normgiff/Masters/DUTBoard/DUTBoardPinout.png

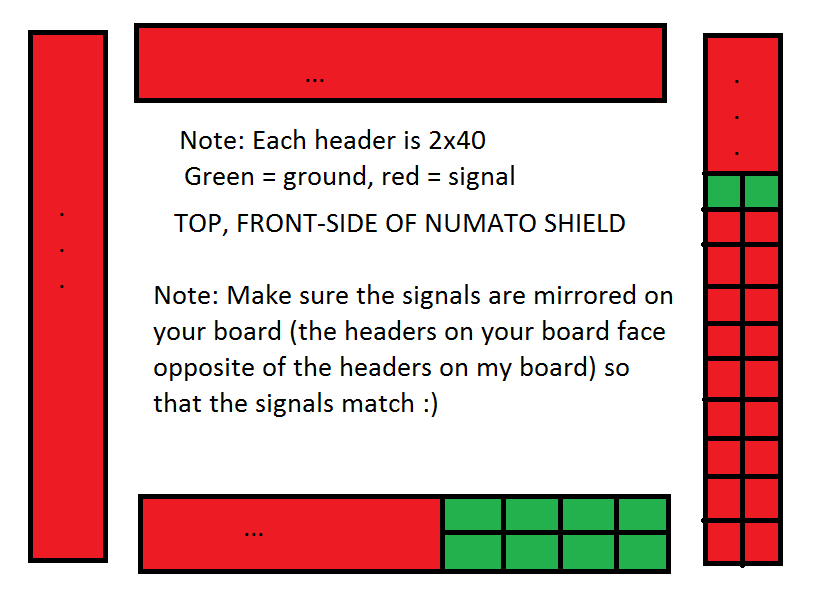
DUTBoard/DUTBoardPinout.png
