normgiff/Masters/explorations/clocking/clocking_proposal.png

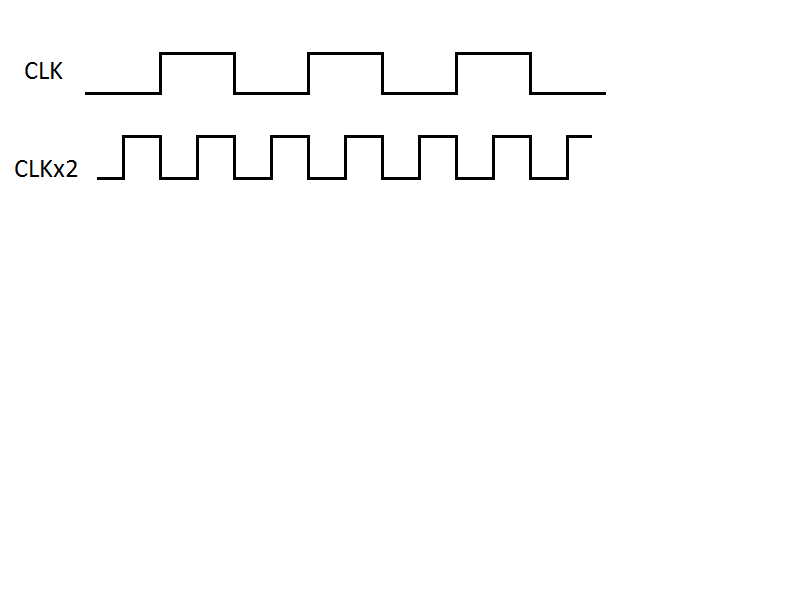
explorations/clocking/clocking_proposal.png
