normgiff/Masters/explorations/clocking/Dynamically_Reconfigurable_PLL.png

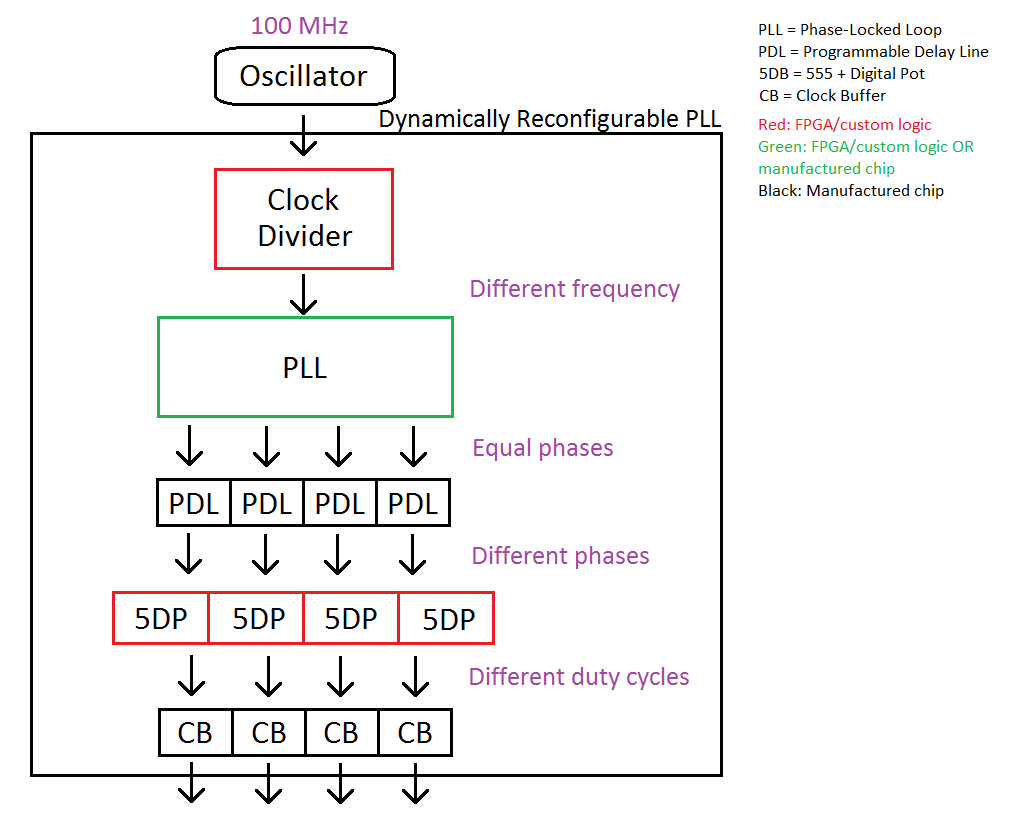
explorations/clocking/Dynamically_Reconfigurable_PLL.png
