normgiff/Masters/explorations/force_formats/force_formats_design_concept_2.png

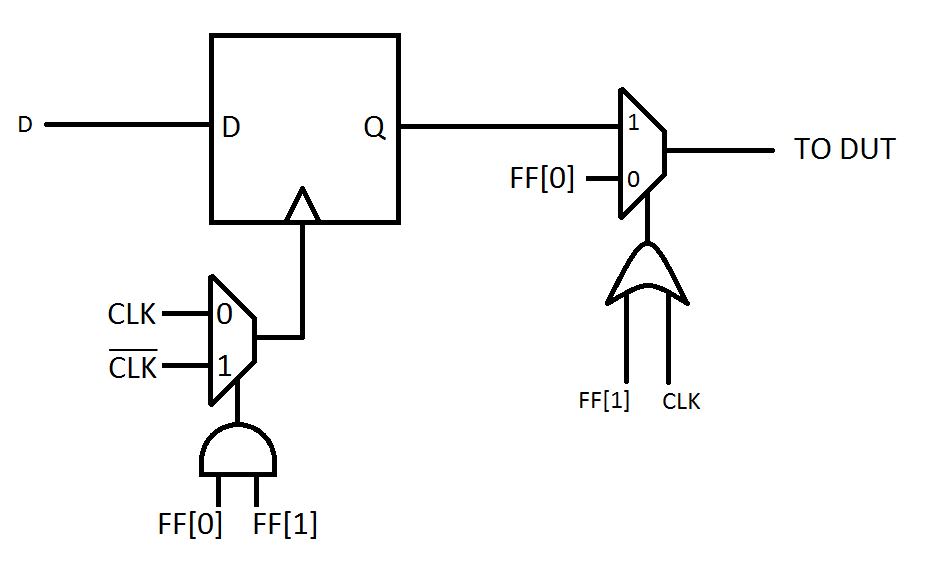
explorations/force_formats/force_formats_design_concept_2.png
