normgiff/Masters/explorations/force_formats/oddr2_idea.png

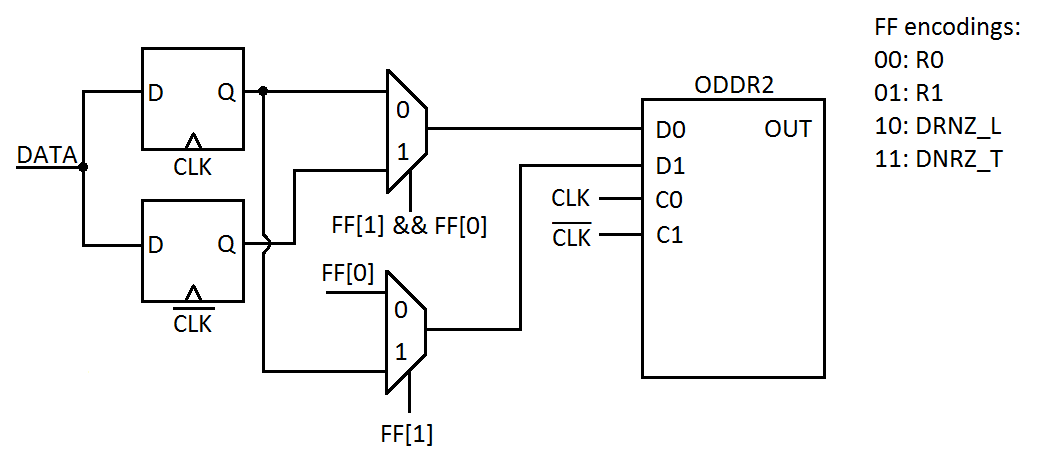
explorations/force_formats/oddr2_idea.png
