normgiff/Masters/explorations/high_level_diagram_1.png

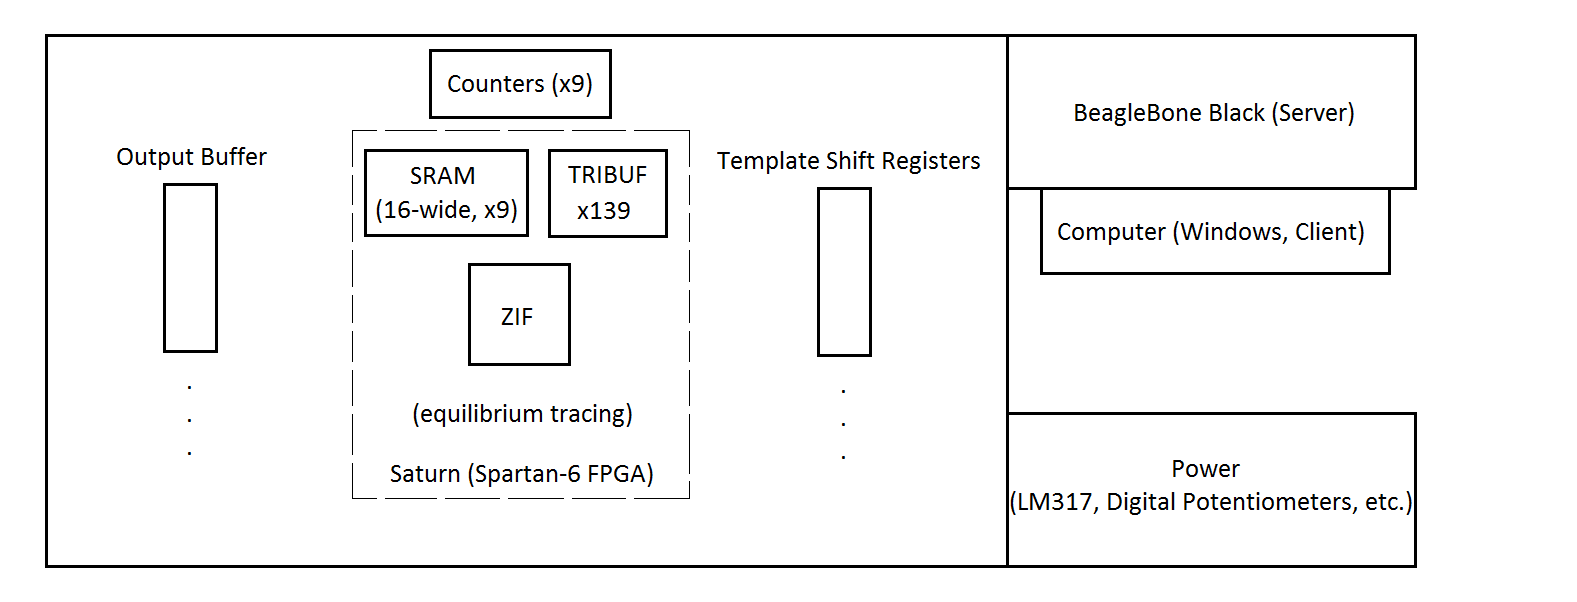
explorations/high_level_diagram_1.png
