normgiff/Masters/explorations/power/idea1.bmp

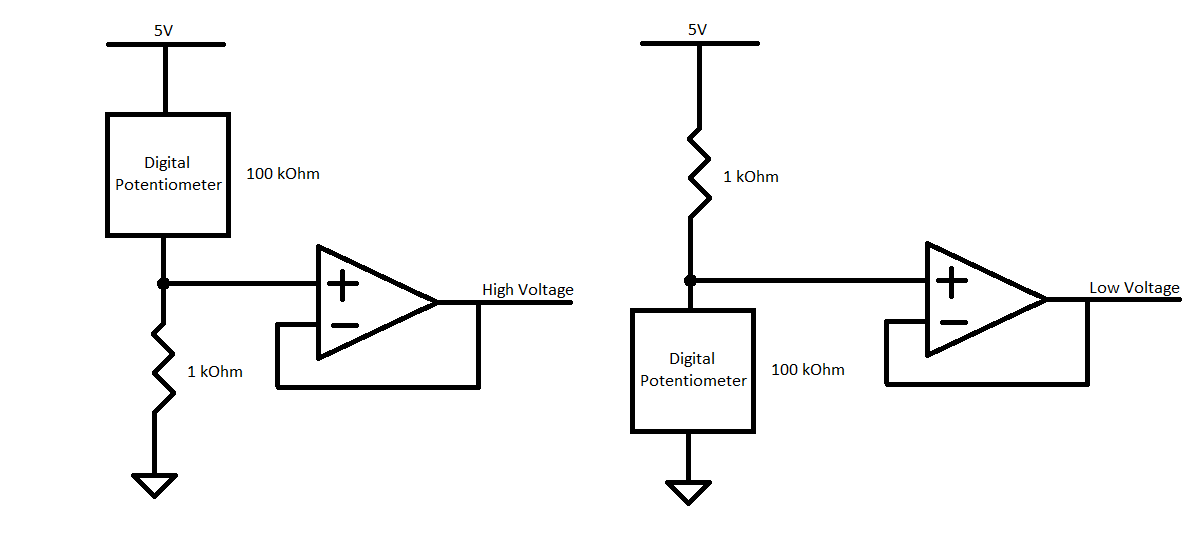
explorations/power/idea1.bmp
