normgiff/Masters/explorations/power/idea2.bmp

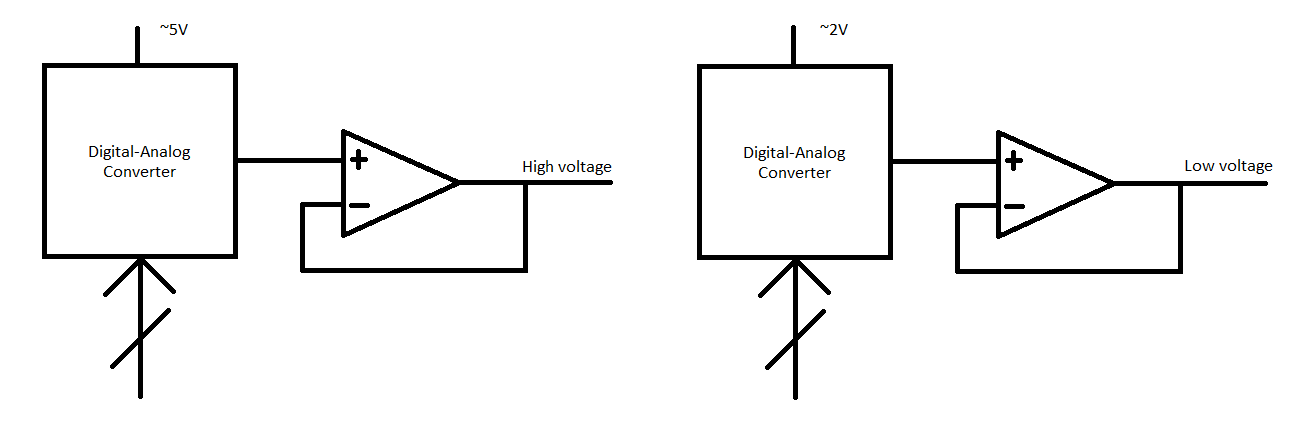
explorations/power/idea2.bmp
