normgiff/Masters/explorations/power/updated_schematic.PNG

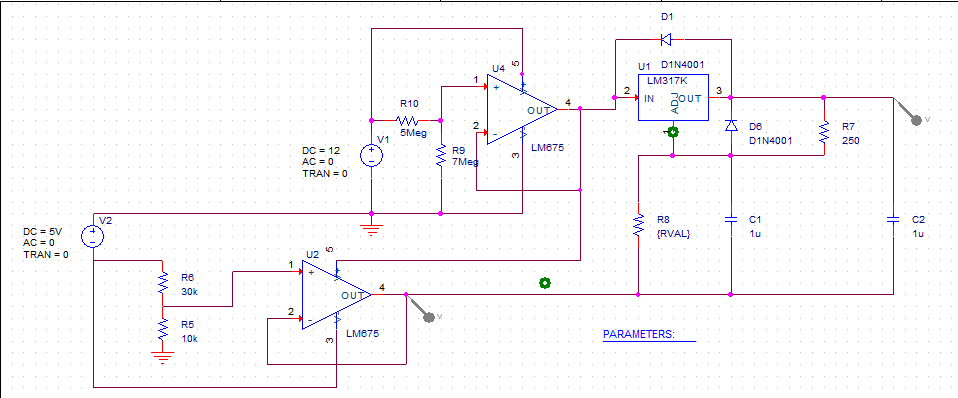
explorations/power/updated_schematic.PNG
