normgiff/Masters/images/boards_3.jpg

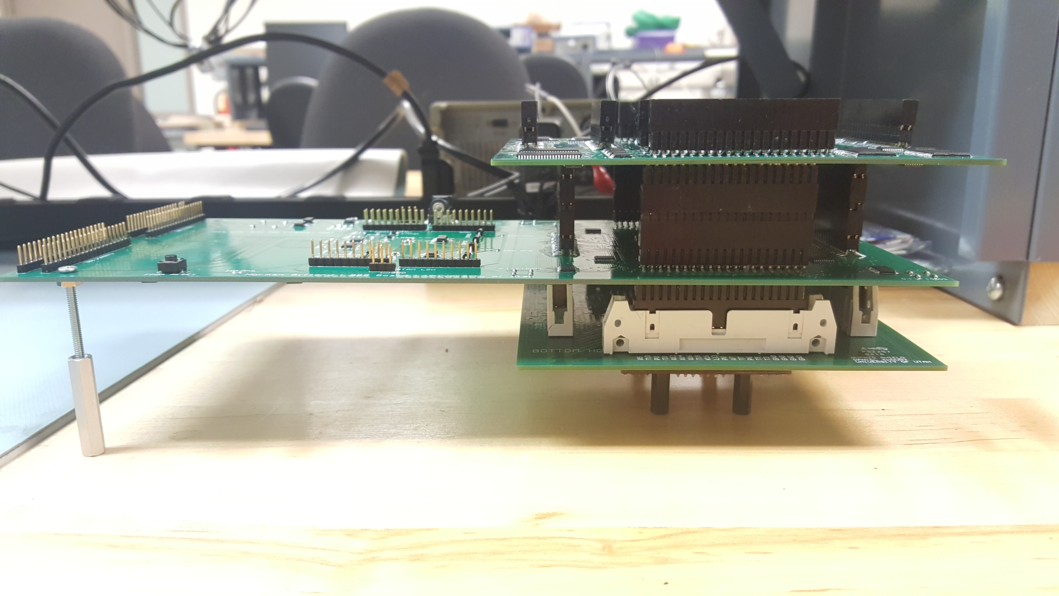
images/boards_3.jpg
