normgiff/Masters/images/headerwithlatch_orig.JPG

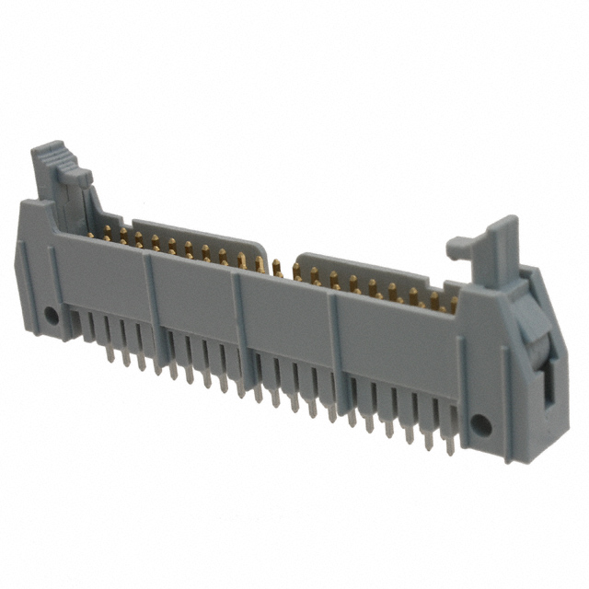
images/headerwithlatch_orig.JPG
