normgiff/Masters/images/mosis_13x13_packages.jpg

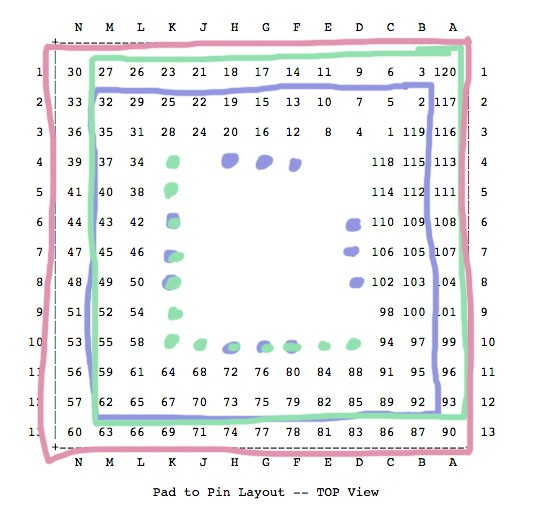
images/mosis_13x13_packages.jpg
