normgiff/Masters/NumatoShield/saturn_dimensions.jpg

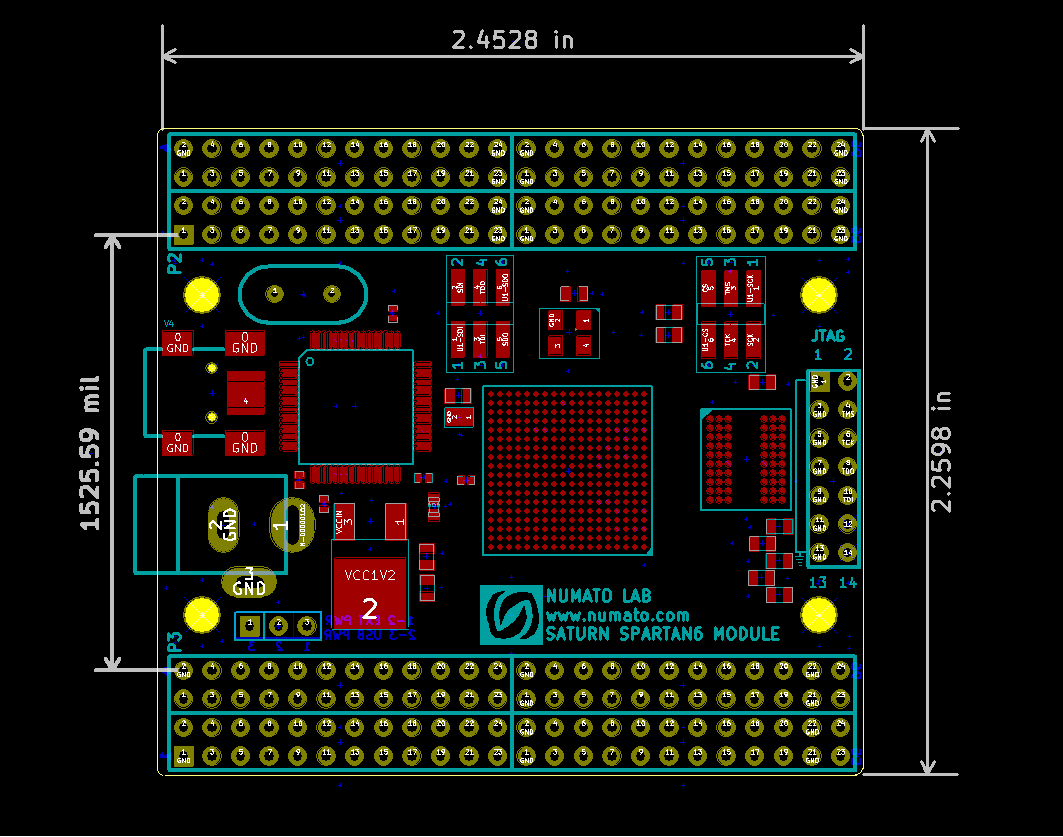
NumatoShield/saturn_dimensions.jpg
