normgiff/Masters/Saturn/saturnpinout.PNG

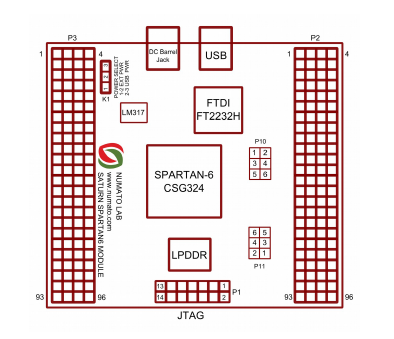
Saturn/saturnpinout.PNG
