normgiff/Masters/schematics/main.png

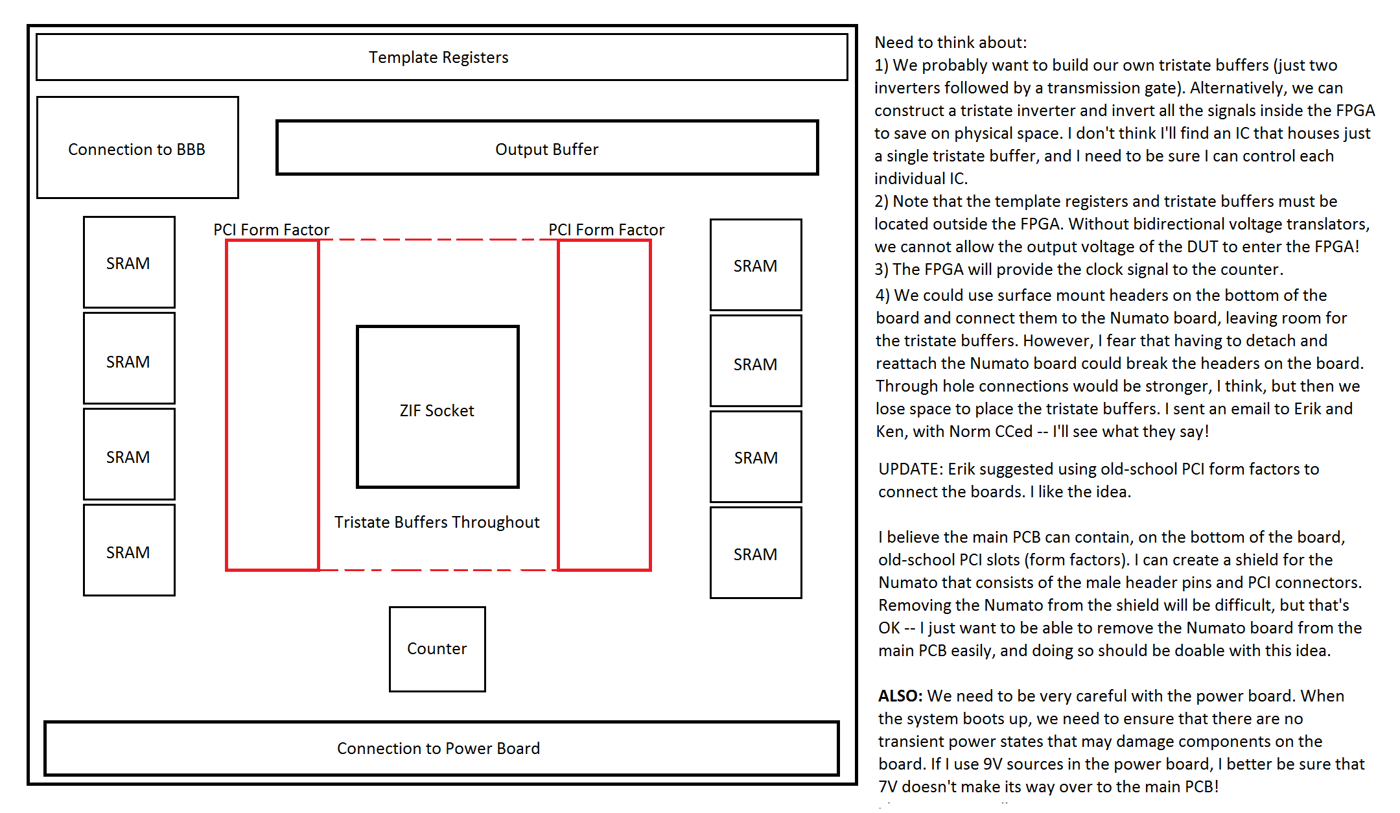
schematics/main.png
