normgiff/Masters/schematics/main_trunc.png

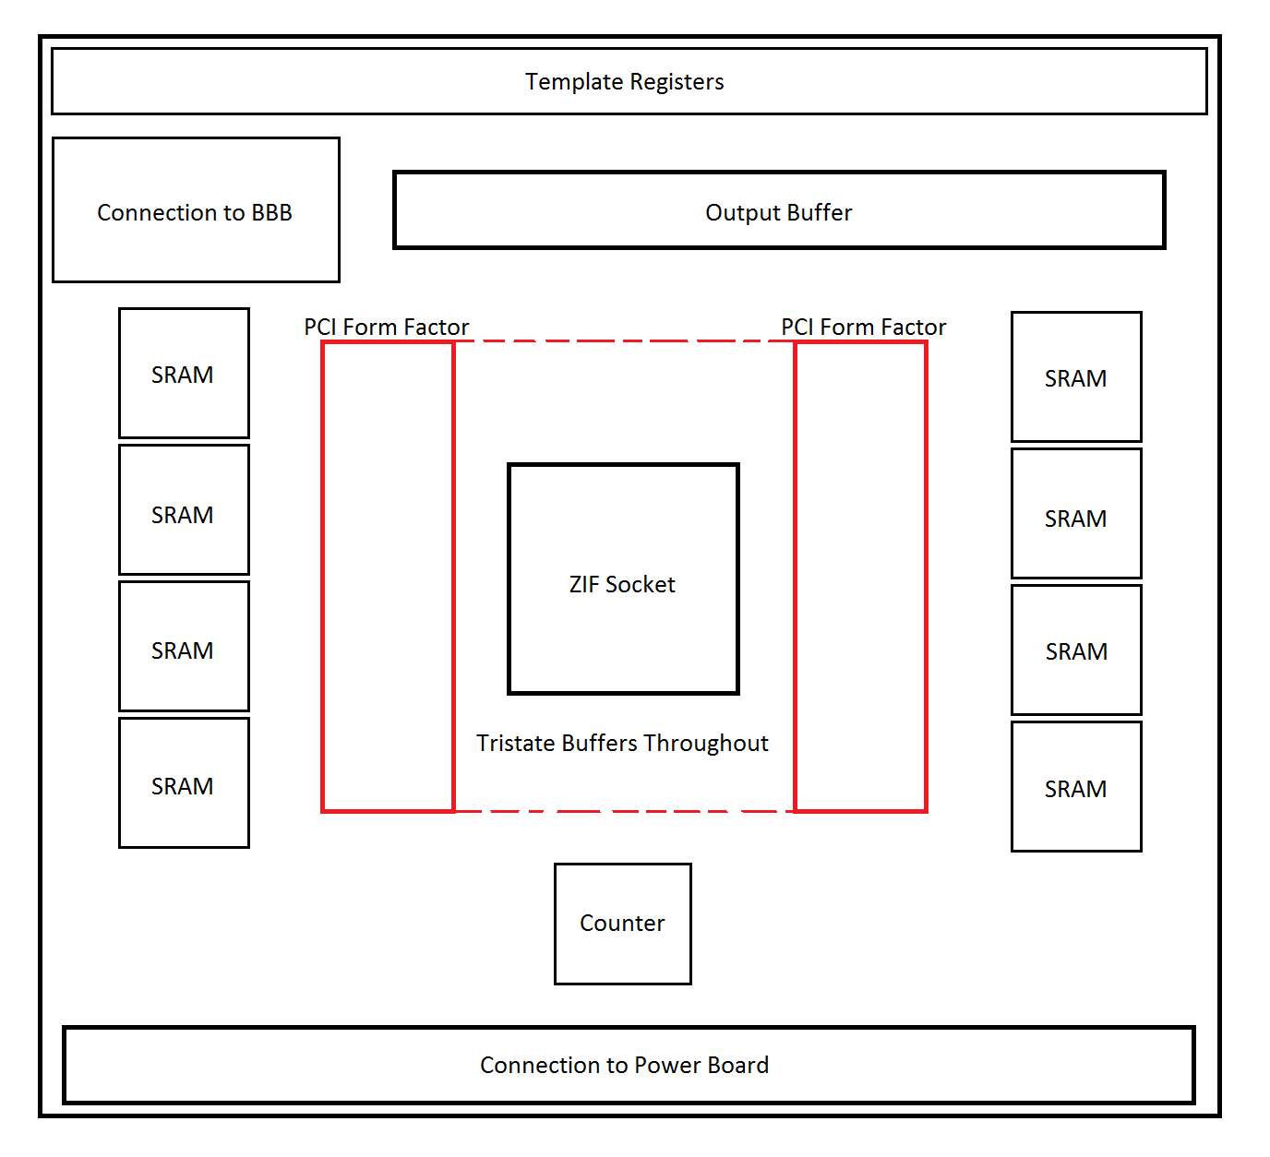
schematics/main_trunc.png
