normgiff/Masters/schematics/power_pcb.png

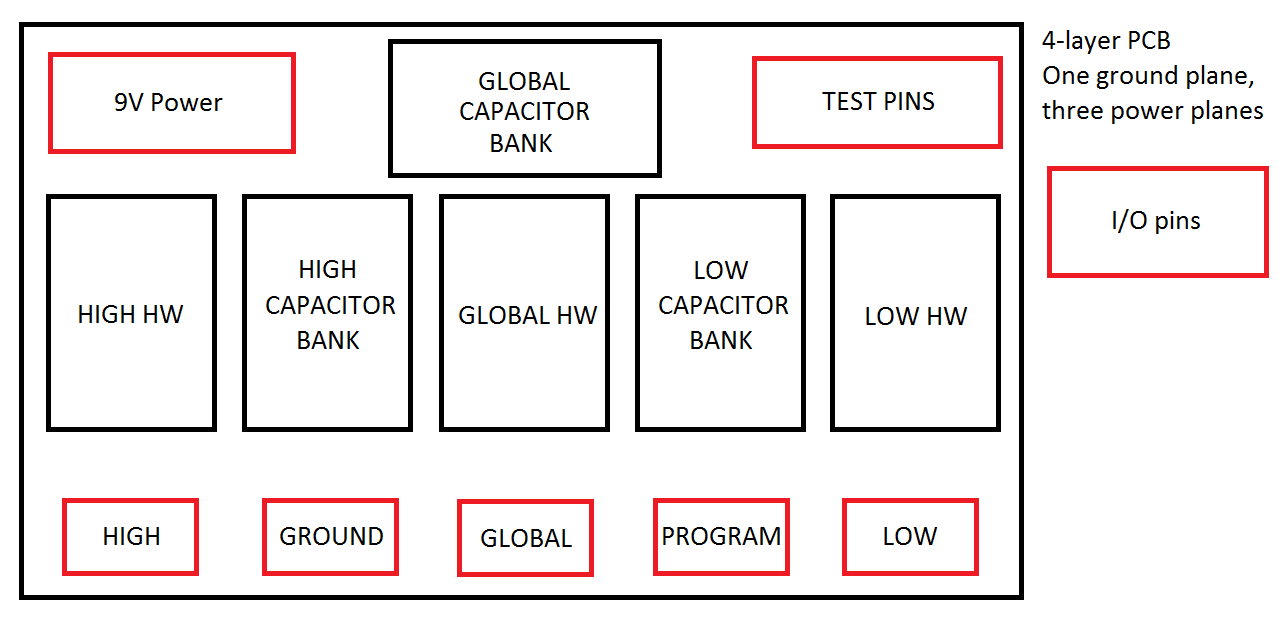
schematics/power_pcb.png
