normgiff/Masters/Verilog/ASICTesterVerilog/CENTRAL_FSM.v

`timescale 1ns / 1ps

// Module: Central finite state machine (FSM).
// Function: Main logic controller.
// 
// This module is very complicated (roughly 60 states).
// We recommend reading through the modules instantiated by this module
// and then studying the comments in this file. 
module CENTRAL_FSM(CLK, RST, 
                   RX, TX,
                   OE_BAR, 
						 CS_BAR_1, WE_BAR_1,
						 CS_BAR_2, WE_BAR_2,
						 CS_BAR_3, WE_BAR_3,
						 CS_BAR_4, WE_BAR_4, 
                   COUNTER_CLK_1, COUNTER_CLK_2, COUNTER_CLK_3, COUNTER_CLK_4, 
				       COUNTER_RST, 
                   MR_BAR, PL_BAR, STCP, SHCP, Q,
                   VT_EN,
				       SIGNALS);

	// Global clock (100 MHz) and reset.
	input CLK;
	input RST;
	
	// UART.
	input RX;
	output TX;
	
	// SRAM.
	// Signals are duplicated for load-balancing.
	output OE_BAR;
	output CS_BAR_1;
	output WE_BAR_1;
	output CS_BAR_2;
	output WE_BAR_2;
	output CS_BAR_3;
	output WE_BAR_3;
	output CS_BAR_4;
	output WE_BAR_4;
	
	// Counter.
	// Signals are duplicated for load-balancing.
	output COUNTER_CLK_1;
	output COUNTER_CLK_2;
	output COUNTER_CLK_3;
	output COUNTER_CLK_4;
	output COUNTER_RST;
	
	// Output buffers (parallel->serial shift registers).
	output MR_BAR;
	output PL_BAR;
	output STCP;
	output SHCP;
	input Q;
	
	// Voltage translators.
	output VT_EN;
	
	// Signals to DUT.
	output [125:0] SIGNALS;
	
	// States and UART codes.
	`include "CENTRAL_FSM_PARAMS.v"

	reg [5:0] PS;
	reg [5:0] NS;
	
	// Present-state logic.
	always@(posedge CLK) begin
		if (RST) begin
			PS <= IDLE;
		end
		else begin
			PS <= NS;
		end
	end
	
	// Soft reset applied after tests are completed.
	wire soft_reset = (PS == TESTS_COMPLETED);
	
	// Note that RST is used in some areas instead of rst.
	assign rst = soft_reset || RST;
	
	// Counter used to change hardware (SRAM, counters) during a test cycle.
	reg [9:0] cycle_length_counter;
	
	// When high, increment the counter ICs.
	reg next_address;
	
	// When high, enable write-mode for SRAM.
	reg turn_on_sram;
	
	// When high, transfer the new signals for the DUT.
	reg transfer_new_signals;
	
	// When high, the test cycle is completed.
	reg end_of_test_cycle;
	
	always@(posedge CLK) begin
		if (rst) begin
			cycle_length_counter <= 10'd0;
			next_address <= 1'b0;
			turn_on_sram <= 1'b0;
			transfer_new_signals <= 1'b0;
			end_of_test_cycle <= 1'b0;
		end
		else begin
			next_address <= 1'b0;
			transfer_new_signals <= 1'b0;
			end_of_test_cycle <= 1'b0;
			
			if (perform_test) begin		
				if (cycle_length_counter == (cycle_length - 1)) begin
					// End of test cycle.
					cycle_length_counter <= 10'd0;
					end_of_test_cycle <= 1'b1;
				end
				else begin
					cycle_length_counter <= cycle_length_counter + 10'd1;
					case (cycle_length_counter)
						leading_edge_1 - 10'd3: begin
							// Turn on SRAM as soon as we start applying inputs.
							turn_on_sram <= 1'b1;
						end
						
						trailing_edge - 10'd3: begin
							// As soon as we hit the trailing edge, turn off the SRAM blocks
							// by raising CS_BAR.
							// It looks like the voltage translators have a delay of 
							// about 20 nanoseconds, so we turn off SRAM three cycles before 
							// the trailing edge.
							turn_on_sram <= 1'b0;
						end
						
						cycle_length - 10'd2: begin
							// Go to the next counter address right at the end of a test cycle.
							// Also, transfer the new signals.
							// NOTE: The counter may increment after the last test cycle is complete.
							//       Not a big deal.
							next_address <= 1'b1;
							transfer_new_signals <= 1'b1;
						end						
						
					endcase
					
				end
			end
			else begin
				// Reset the counter if we need to halt a test, or if testing is complete.
				cycle_length_counter <= 10'd0;
			end
		end
	end
	
	// Next-state logic.
	always@(*) begin
		NS = IDLE;
		
		case (PS)			
			IDLE: begin
				if (rxdata_ready) begin
					NS = DECODE_UART_CODE;
				end
				else begin
					NS = IDLE;
				end
			end
			
			DECODE_UART_CODE: begin
				case (rxdata[7:0])
					// Analyze the received UART code. See UART_CTRL.v for more information
					// on the BBB-FPGA protocol.
					
					TEMPLATE_HDR: begin
						NS = PREPARE_FOR_TEMPLATE_VECTOR_1;
					end
					
					INPUT_HDR: begin
						NS = PREPARE_FOR_INPUT_VECTOR_1;
					end
					
					CYCLE_HDR: begin
						NS = PREPARE_FOR_CYCLE_VECTOR_1;
					end
					
					FF_HDR: begin
						NS = PREPARE_FOR_FF_VECTOR_1;
					end
					
					CYCLE_CONFIG_HDR: begin
						NS = STORE_CYCLE_CONFIG_DATA;
					end
					
					EXECUTE_TESTS: begin
						if (more_to_read) begin
							NS = RESET_HARDWARE_PRETEST;
						end
						else begin
							NS = UART_CAPTURE_NO_TESTS;
						end
					end
					
					SEND_BACK_DATA: begin
						NS = LOAD_SRAM_DATA_0;
					end
					
					default: begin
						// Unknown command received.
						NS = UART_CAPTURE_UNKNOWN_CODE;
					end
				
				endcase
			end
			
			//////////////////////////////////////////
			// Reading and storing template vector. //
			//////////////////////////////////////////
			
			PREPARE_FOR_TEMPLATE_VECTOR_1: begin
				NS = PREPARE_FOR_TEMPLATE_VECTOR_2;
			end
			
			PREPARE_FOR_TEMPLATE_VECTOR_2: begin
				NS = WAIT_FOR_TEMPLATE_VECTOR_1;
			end
			
			WAIT_FOR_TEMPLATE_VECTOR_1: begin
				if (txsent) begin
					NS = WAIT_FOR_TEMPLATE_VECTOR_2;
				end
				else begin
					NS = WAIT_FOR_TEMPLATE_VECTOR_1;
				end
			end
			
			WAIT_FOR_TEMPLATE_VECTOR_2: begin
				if (rxdata_ready) begin
					NS = STORE_TEMPLATE_VECTOR_1;
				end
				else begin
					NS = WAIT_FOR_TEMPLATE_VECTOR_2;
				end
			end
			
			STORE_TEMPLATE_VECTOR_1: begin
				NS = STORE_TEMPLATE_VECTOR_2;				
			end
			
			STORE_TEMPLATE_VECTOR_2: begin
				if (bram_ctrl_ready) begin
					NS = UART_CAPTURE_ACK;
				end
				else begin
					NS = STORE_TEMPLATE_VECTOR_2;
				end
			end
			
			///////////////////////////////////////
			// Reading and storing input vector. //
			///////////////////////////////////////
			
			PREPARE_FOR_INPUT_VECTOR_1: begin
				NS = PREPARE_FOR_INPUT_VECTOR_2;
			end
			
			PREPARE_FOR_INPUT_VECTOR_2: begin
				NS = WAIT_FOR_INPUT_VECTOR_1;
			end
			
			WAIT_FOR_INPUT_VECTOR_1: begin
				if (txsent) begin
					NS = WAIT_FOR_INPUT_VECTOR_2;
				end
				else begin
					NS = WAIT_FOR_INPUT_VECTOR_1;
				end
			end
			
			WAIT_FOR_INPUT_VECTOR_2: begin
				if (rxdata_ready) begin
					NS = STORE_INPUT_VECTOR_1;
				end
				else begin
					NS = WAIT_FOR_INPUT_VECTOR_2;
				end
			end
			
			STORE_INPUT_VECTOR_1: begin
				NS = STORE_INPUT_VECTOR_2;				
			end
			
			STORE_INPUT_VECTOR_2: begin
				if (bram_ctrl_ready) begin
					NS = UART_CAPTURE_ACK;
				end
				else begin
					NS = STORE_INPUT_VECTOR_2;
				end
			end
			
			///////////////////////////////////////
			// Reading and storing cycle vector. //
			///////////////////////////////////////
			
			PREPARE_FOR_CYCLE_VECTOR_1: begin
				NS = PREPARE_FOR_CYCLE_VECTOR_2;
			end
			
			PREPARE_FOR_CYCLE_VECTOR_2: begin
				NS = WAIT_FOR_CYCLE_VECTOR_1;
			end
			
			WAIT_FOR_CYCLE_VECTOR_1: begin
				if (txsent) begin
					NS = WAIT_FOR_CYCLE_VECTOR_2;
				end
				else begin
					NS = WAIT_FOR_CYCLE_VECTOR_1;
				end
			end
			
			WAIT_FOR_CYCLE_VECTOR_2: begin
				if (rxdata_ready) begin
					NS = STORE_CYCLE_VECTOR_1;
				end
				else begin
					NS = WAIT_FOR_CYCLE_VECTOR_2;
				end
			end
			
			STORE_CYCLE_VECTOR_1: begin
				NS = STORE_CYCLE_VECTOR_2;				
			end
			
			STORE_CYCLE_VECTOR_2: begin
				if (bram_ctrl_ready) begin
					NS = UART_CAPTURE_ACK;
				end
				else begin
					NS = STORE_CYCLE_VECTOR_2;
				end
			end
			
			//////////////////////////////////////////////
			// Reading and storing force-format vector. //
			//////////////////////////////////////////////
			
			PREPARE_FOR_FF_VECTOR_1: begin
				NS = PREPARE_FOR_FF_VECTOR_2;
			end
			
			PREPARE_FOR_FF_VECTOR_2: begin
				NS = WAIT_FOR_FF_VECTOR_1;
			end
			
			WAIT_FOR_FF_VECTOR_1: begin
				if (txsent) begin
					NS = WAIT_FOR_FF_VECTOR_2;
				end
				else begin
					NS = WAIT_FOR_FF_VECTOR_1;
				end
			end
			
			WAIT_FOR_FF_VECTOR_2: begin
				if (rxdata_ready) begin
					NS = STORE_FF_VECTOR_1;
				end
				else begin
					NS = WAIT_FOR_FF_VECTOR_2;
				end
			end
			
			STORE_FF_VECTOR_1: begin
				NS = STORE_FF_VECTOR_2;				
			end
			
			STORE_FF_VECTOR_2: begin
				if (bram_ctrl_ready) begin
					NS = UART_CAPTURE_ACK;
				end
				else begin
					NS = STORE_FF_VECTOR_2;
				end
			end
			
			///////////////////////////////
			// Cycle configuration data. //
			///////////////////////////////
			
			STORE_CYCLE_CONFIG_DATA: begin
				NS = UART_CAPTURE_ACK;
			end
			
			///////////////////////
			// Performing tests. //
			///////////////////////
			
			RESET_HARDWARE_PRETEST: begin
				if (counter_busy) begin
					NS = RESET_HARDWARE_PRETEST;
				end
				else begin
					NS = READ_INPUT_VECTOR_1;
				end
			end
			
			READ_INPUT_VECTOR_1: begin
				NS = READ_INPUT_VECTOR_2;
			end
			
			READ_INPUT_VECTOR_2: begin
				if (bram_ctrl_ready) begin
					NS = LOAD_INPUT_VECTOR;
				end
				else begin
					NS = READ_INPUT_VECTOR_2;
				end
			end
			
			LOAD_INPUT_VECTOR: begin
				NS = TRANSFER_INPUT_VECTOR;
			end
			
			TRANSFER_INPUT_VECTOR: begin
				// Must transfer the input vector before we load
				// the FF registers.
				if (perform_test) begin
					NS = CHECK_INPUT_VECTOR;
				end
				else begin
					// We haven't begun testing yet. Load all other vectors 
					// associated with the input vector's template.
					NS = READ_TEMPLATE_VECTOR_1;
				end
			end
			
			READ_TEMPLATE_VECTOR_1: begin
				NS = READ_TEMPLATE_VECTOR_2;
			end
			
			READ_TEMPLATE_VECTOR_2: begin
				if (bram_ctrl_ready) begin
					NS = LOAD_TEMPLATE_VECTOR;
				end
				else begin
					NS = READ_TEMPLATE_VECTOR_2;
				end
			end
			
			LOAD_TEMPLATE_VECTOR: begin
				NS = READ_CYCLE_VECTOR_1;
			end
			
			READ_CYCLE_VECTOR_1: begin
				NS = READ_CYCLE_VECTOR_2;
			end
			
			READ_CYCLE_VECTOR_2: begin
				if (bram_ctrl_ready) begin
					NS = LOAD_CYCLE_VECTOR;
				end
				else begin
					NS = READ_CYCLE_VECTOR_2;
				end
			end
			
			LOAD_CYCLE_VECTOR: begin
				NS = READ_FF_VECTOR_1;
			end
			
			READ_FF_VECTOR_1: begin
				NS = READ_FF_VECTOR_2;
			end
			
			READ_FF_VECTOR_2: begin
				if (bram_ctrl_ready) begin
					NS = LOAD_FF_VECTOR;
				end
				else begin
					NS = READ_FF_VECTOR_2;
				end
			end
			
			LOAD_FF_VECTOR: begin
				NS = TRANSFER_VECTORS;
			end
			
			TRANSFER_VECTORS: begin
				NS = CHECK_FOR_MORE_INPUT_VECTORS;
			end
			
			CHECK_FOR_MORE_INPUT_VECTORS: begin
				if (more_to_read) begin
					NS = READ_INPUT_VECTOR_1;				
				end
				else begin
					if (end_of_test_cycle) begin
						NS = TESTS_COMPLETED;
					end
					else begin
						NS = CHECK_FOR_MORE_INPUT_VECTORS;
					end
				end
			end
			
			CHECK_INPUT_VECTOR: begin
				if (template_change && end_of_test_cycle) begin
					// Halt real-time testing, load the new configuration bits.
					// The new input vector has already been loaded and transferred.
					NS = READ_TEMPLATE_VECTOR_1;
				end
				else begin
					// Transfer the new signal bits to the FF registers
					// once the test cycle is complete.
					if (!template_change && transfer_new_signals) begin
						NS = TRANSFER_VECTORS;
					end
					else begin
						NS = CHECK_INPUT_VECTOR;
					end
				end
			end
			
			TESTS_COMPLETED: begin
				// The tests have been completed.
				// Perform a soft reset, which also resets the counters, turns off SRAM blocks, 
				// disables all tristates, and disables voltage translators.
				// Then, clear the UART read buffer and transmit an acknowledgement.
				NS = UART_CAPTURE_ACK;
			end

			LOAD_SRAM_DATA_0: begin
				NS = LOAD_SRAM_DATA_1;
			end

			LOAD_SRAM_DATA_1: begin
				NS = LOAD_SRAM_DATA_2;
			end
			
			LOAD_SRAM_DATA_2: begin
				NS = LOAD_SRAM_DATA_3;
			end
			
			LOAD_SRAM_DATA_3: begin
				NS = LOAD_SRAM_DATA_4;
			end
			
			LOAD_SRAM_DATA_4: begin
				NS = LOAD_SRAM_DATA_5;
			end
			
			LOAD_SRAM_DATA_5: begin
				// Wait for the SRAM data to be loaded.
				if (output_buffer_ctrl_ready) begin
					NS = TRANSMIT_SRAM_DATA;
				end
				else begin
					NS = LOAD_SRAM_DATA_5; 
				end
			end
			
			TRANSMIT_SRAM_DATA: begin
				NS = UART_TRANSMIT_1;
			end
					
			/////////////////////////////////////
			// General UART code transmission. //
			/////////////////////////////////////
			
			UART_CAPTURE_ACK: begin
				NS = UART_TRANSMIT_1;
			end
			
			UART_CAPTURE_UNKNOWN_CODE: begin
				NS = UART_TRANSMIT_1;
			end
			
			UART_CAPTURE_NO_TESTS: begin
				NS = UART_TRANSMIT_1;
			end
			
			UART_TRANSMIT_1: begin
				NS = UART_TRANSMIT_2;
			end
			
			UART_TRANSMIT_2: begin
				if (txsent) begin
					NS = IDLE;
				end
				else begin
					NS = UART_TRANSMIT_2;
				end
			end
			
		endcase
	
	end
	
	///////////////////////////////////
	// Modules and associated logic. //
	///////////////////////////////////
	
	// Block RAM controller.
	reg input_write;
	reg template_write;
	reg ff_write;
	reg tc_write;
	reg [127:0] write_data;
	reg template_read;
	reg [1:0] template_bits;
	reg input_read;
	reg ff_read;
	reg tc_read;
	wire [127:0] read_data;
	wire template_change;
	wire bram_ctrl_ready;
	wire more_to_read;
	
	// Used to determine if we need to switch templates.
	reg [1:0] current_template_bits;
	
	always@(posedge CLK) begin
		if (rst) begin
			current_template_bits <= 2'b0;
		end
		else begin
			case (PS) 
				READ_INPUT_VECTOR_2: begin
					if (bram_ctrl_ready) begin
						current_template_bits <= read_data[127:126];
					end
				end
			endcase
		end
	end
	
	always@(*) begin
		template_write = 1'b0;
		input_write = 1'b0;
		ff_write = 1'b0;
		tc_write = 1'b0;
		write_data = 128'b0;
		
		template_read = 1'b0;
		template_bits = current_template_bits;
		input_read = 1'b0;
		ff_read = 1'b0;
		tc_read = 1'b0;
			
		case(PS)
		
			STORE_TEMPLATE_VECTOR_1: begin
				template_write = 1'b1;
				write_data = rxdata;
			end
			
			STORE_TEMPLATE_VECTOR_2: begin
				write_data = rxdata;
			end
			
			STORE_INPUT_VECTOR_1: begin
				input_write = 1'b1;
				write_data = rxdata;
			end
			
			STORE_INPUT_VECTOR_2: begin
				write_data = rxdata;
			end
			
			STORE_CYCLE_VECTOR_1: begin
				tc_write = 1'b1;
				write_data = rxdata;
			end
			
			STORE_CYCLE_VECTOR_2: begin
				write_data = rxdata;
			end
			
			STORE_FF_VECTOR_1: begin
				ff_write = 1'b1;
				write_data = rxdata;
			end
			
			STORE_FF_VECTOR_2: begin
				write_data = rxdata;
			end
			
			READ_INPUT_VECTOR_1: begin
				input_read = 1'b1;
			end
			
			READ_TEMPLATE_VECTOR_1: begin
				template_read = 1'b1;
			end
			
			READ_CYCLE_VECTOR_1: begin
				tc_read = 1'b1;
			end
			
			READ_FF_VECTOR_1: begin
				ff_read = 1'b1;
			end
			
		endcase
		
	end
	
	BRAM_CTRL bram_ctrl0(
								.CLK(CLK), 
								.RST(RST), 
								.RESET_READ_COUNTER(soft_reset),
								.INPUT_WRITE(input_write), 
								.TEMPLATE_WRITE(template_write), 
								.FF_WRITE(ff_write), 
								.TC_WRITE(tc_write),
								.WRITE_DATA(write_data), 
								.TEMPLATE_READ(template_read), 
								.TEMPLATE_BITS(template_bits), 
								.INPUT_READ(input_read), 
								.FF_READ(ff_read), 
								.TC_READ(tc_read),
								.READ_DATA(read_data), 
								.TEMPLATE_CHANGE(template_change), 
								.READY(bram_ctrl_ready),
								.MORE_TO_READ(more_to_read)
								);								
	
	// Counter controller.
	reg advance_counter;
	reg reset_counter;
	wire counter_busy;
	
	always@(posedge CLK) begin
		if (rst) begin
			advance_counter <= 1'b0;
			reset_counter <= 1'b1;
		end
		else begin
			advance_counter <= 1'b0;
			reset_counter <= 1'b0;
			
			case (PS)
				RESET_HARDWARE_PRETEST: begin
					reset_counter <= 1'b1;
				end
				
				TESTS_COMPLETED: begin
					reset_counter <= 1'b1;
				end
				
				TRANSMIT_SRAM_DATA: begin
					// Advance the counter for the next time SRAM data is requested.
					advance_counter <= 1'b1;
				end
				
				default: begin
					if (next_address) begin
						advance_counter <= 1'b1;
					end
				end

			endcase	
		end
	end
	
	COUNTER_CTRL counter_ctrl0(
										.CLK(CLK), 
										.RST(rst), 
										.ADVANCE_COUNTER(advance_counter), 
										.RESET_COUNTER(reset_counter), 
										.COUNTER_CLK_1(COUNTER_CLK_1), 
										.COUNTER_CLK_2(COUNTER_CLK_2), 
										.COUNTER_CLK_3(COUNTER_CLK_3), 
										.COUNTER_CLK_4(COUNTER_CLK_4), 
										.COUNTER_RST(COUNTER_RST),
										.BUSY(counter_busy)
										);
										
	// DUT controller.
	reg perform_test;
	wire [125:0] bus126;
	reg sig_load;
	reg sig_transfer;
	reg ff_load_ff;
	reg ff_transfer_ff;
	reg ff_load_sig;
	reg ff_transfer_sig;
	reg template_load;
	reg template_transfer;
	reg cycle_load;
	reg cycle_transfer;
	reg [9:0] leading_edge_1;
	reg [9:0] leading_edge_2;
	reg [9:0] trailing_edge;
	reg [9:0] cycle_length;
	
	assign bus126 = read_data[125:0];
	
	// Logic to store cycle configuration parameters.
	// Some default values provided.
	always@(posedge CLK) begin
		if (RST) begin
			leading_edge_1 <= 10'd600;
			leading_edge_2 <= 10'd650;
			trailing_edge <= 10'd900;
			cycle_length <= 10'd1000;
		end
		else if (PS == STORE_CYCLE_CONFIG_DATA) begin
			leading_edge_1 <= rxdata[17:8];
			leading_edge_2 <= rxdata[33:24];
			trailing_edge <= rxdata[49:40];
			cycle_length <= rxdata[65:56];
		end
	end
	
	always@(posedge CLK) begin
		if (rst) begin
			perform_test <= 1'b0;
		end
		else if (PS == TRANSFER_VECTORS) begin
			perform_test <= 1'b1;
		end
		else if (PS == CHECK_INPUT_VECTOR) begin
			if (template_change && end_of_test_cycle) begin
				perform_test <= 1'b0;
			end
		end
	end
	
	always@(*) begin
		sig_load = 1'b0;
		sig_transfer = 1'b0;
		ff_load_ff = 1'b0;
		ff_transfer_ff = 1'b0;
		ff_load_sig = 1'b0;
		ff_transfer_sig = 1'b0;
		template_load = 1'b0;
		template_transfer = 1'b0;
		cycle_load = 1'b0;
		cycle_transfer = 1'b0;
	
		case (PS)
			LOAD_INPUT_VECTOR: begin
				sig_load = 1'b1;
			end
			
			LOAD_TEMPLATE_VECTOR: begin
				template_load = 1'b1;
			end
			
			LOAD_CYCLE_VECTOR: begin
				cycle_load = 1'b1;
			end
			
			LOAD_FF_VECTOR: begin
				ff_load_ff = 1'b1;
				ff_load_sig = 1'b1;
			end
			
			CHECK_INPUT_VECTOR: begin
				// Ready the FF registers, 
				// whether or not we halt real-time testing.
				if (NS != CHECK_INPUT_VECTOR) begin
					ff_load_sig = 1'b1;
				end
			end
			
			TRANSFER_INPUT_VECTOR: begin
				sig_transfer = 1'b1;
			end
			
			TRANSFER_VECTORS: begin
				template_transfer = 1'b1;
				cycle_transfer = 1'b1;
				ff_transfer_ff = 1'b1;
				ff_transfer_sig = 1'b1;
			end
			
		endcase
	end
	
	DUT_CTRL dut_ctrl0(
							 .CLK(CLK), 
							 .RST(rst), 
							 .PERFORM_TEST(perform_test), 
							 .BUS126(bus126), 
							 .SIG_LOAD(sig_load), 
							 .SIG_TRANSFER(sig_transfer), 
							 .FF_LOAD_FF(ff_load_ff), 
							 .FF_TRANSFER_FF(ff_transfer_ff), 
							 .FF_LOAD_SIG(ff_load_sig), 
							 .FF_TRANSFER_SIG(ff_transfer_sig), 
							 .TEMPLATE_LOAD(template_load), 
							 .TEMPLATE_TRANSFER(template_transfer),
							 .CYCLE_LOAD(cycle_load), 
							 .CYCLE_TRANSFER(cycle_transfer),
							 .LEADING_EDGE_1(leading_edge_1),
							 .LEADING_EDGE_2(leading_edge_2), 
							 .TRAILING_EDGE(trailing_edge), 
							 .CYCLE_LENGTH(cycle_length), 
							 .OUTPUT_SIGNALS(SIGNALS)
							 );
							 
	// Output buffer controller.
	reg clear_buffer;
	reg capture_sram_data;
	wire output_buffer_ctrl_ready;
	wire [127:0] sram_data;
	
	always@(posedge CLK) begin
		if (rst) begin
			clear_buffer <= 1'b1;
			capture_sram_data <= 1'b0;
		end
		else begin
			clear_buffer <= 1'b0;
			capture_sram_data <= 1'b0;
			
			if (output_buffer_ctrl_ready) begin
			
				if (PS == LOAD_SRAM_DATA_3) begin
					capture_sram_data <= 1'b1;
				end
				
			end
		end
	end
		
	OUTPUT_BUFFER_CTRL output_buffer_ctrl0(
													   .CLK(CLK), 
														.RST(RST), 
														.CLEAR_BUFFER(clear_buffer), 
														.CAPTURE_SRAM_DATA(capture_sram_data), 
														.READY(output_buffer_ctrl_ready), 
														.SRAM_DATA(sram_data), 
														.Q(Q), 
														.MR_BAR(MR_BAR), 
														.PL_BAR(PL_BAR), 
														.SHCP(SHCP), 
														.STCP(STCP)
														);
														
	// SRAM controller.
	reg oe_bar_in;
	reg cs_bar_in;
	reg we_bar_in;
	
	always@(posedge CLK) begin
		if (RST) begin
			oe_bar_in <= 1'b1; // Outputs should be disabled by default.
			cs_bar_in <= 1'b1; // Leave off by default.
			we_bar_in <= 1'b0; // Write-mode by default is better to prevent multiple-driver issues.
		end
		else begin		
			case (PS)
				IDLE: begin
					// Write-mode by default is better to prevent multiple-driver issues.
					oe_bar_in <= 1'b1;
					cs_bar_in <= 1'b1;
					we_bar_in <= 1'b0;
				end
			
				RESET_HARDWARE_PRETEST: begin
					// Disable outputs so we can write to them.
					// Set to write mode, but keep the device off (via CS).
					oe_bar_in <= 1'b0;
					cs_bar_in <= 1'b1;
					we_bar_in <= 1'b0;
				end
				
				TESTS_COMPLETED: begin
					// Turn off the SRAM blocks.
					oe_bar_in <= 1'b1;
					cs_bar_in <= 1'b1;
					we_bar_in <= 1'b0;
				end
				
				LOAD_SRAM_DATA_1: begin
					// Enable reading mode.
					we_bar_in <= 1'b1;
				end
				
				LOAD_SRAM_DATA_2: begin
					// Turn on the SRAM blocks.
					cs_bar_in <= 1'b0;
				end
				
				LOAD_SRAM_DATA_3: begin
					// Outputs in driving state.
					oe_bar_in <= 1'b0;
				end
				
				LOAD_SRAM_DATA_4: begin
					// Do nothing.
				end
				
				LOAD_SRAM_DATA_5: begin
					// Nothing.
				end
				
				
				TRANSMIT_SRAM_DATA: begin
					// We can turn off the SRAM blocks now, as
					// the data has been captured.
					// Turn off write in the next cycle, to avoid glitches.
					oe_bar_in <= 1'b1;
					cs_bar_in <= 1'b1;
				end	

				default: begin
					if (turn_on_sram) begin
						cs_bar_in <= 1'b0;
					end	
					else begin
						cs_bar_in <= 1'b1;
					end
				end
			endcase
		end
	end
	
	SRAM_CTRL sram_ctrl_0(
								 .CLK(CLK),
								 .RST(RST),
								 .OE_BAR_IN(oe_bar_in), 
								 .CS_BAR_IN(cs_bar_in), 
								 .WE_BAR_IN(we_bar_in), 
								 .OE_BAR(OE_BAR), 
								 .CS_BAR_1(CS_BAR_1), 
								 .WE_BAR_1(WE_BAR_1),
								 .CS_BAR_2(CS_BAR_2), 
								 .WE_BAR_2(WE_BAR_2),
								 .CS_BAR_3(CS_BAR_3), 
								 .WE_BAR_3(WE_BAR_3),
								 .CS_BAR_4(CS_BAR_4), 
								 .WE_BAR_4(WE_BAR_4)
								 );

	// UART controller.
	wire rxdata_ready;
	reg rxdata_retrieved;
	wire [127:0] rxdata;
	reg [127:0] txdata;
	reg txcapture;
	reg txtransmit;
	wire txsent;
	reg txack;
	
	always@(*) begin
		rxdata_retrieved = 1'b0;
		txcapture = 1'b0;
		txtransmit = 1'b0;
		txack = 1'b0;
		txdata = 128'd0;
		
		case (PS)
			//////////////////////////////////////////
			// Reading and storing template vector. //
			//////////////////////////////////////////
			
			PREPARE_FOR_TEMPLATE_VECTOR_1: begin
				// Clear the UART read buffer.
				rxdata_retrieved = 1'b1;
				
				// Ready the UART controller for transmission of acknowledgement.
				txdata = {120'b0, ACKNOWLEDGE};
				txcapture = 1'b1;
			end
			
			PREPARE_FOR_TEMPLATE_VECTOR_2: begin
				// Transmit the acknowledgement to the BBB.
				txtransmit = 1'b1;
			end
			
			WAIT_FOR_TEMPLATE_VECTOR_1: begin
				// Acknowledge completion of the transmission.
				if (txsent) begin
					txack = 1'b1;
				end
			end
			
			WAIT_FOR_TEMPLATE_VECTOR_2: begin
				// Wait until the template vector arrives.
			end
		
			STORE_TEMPLATE_VECTOR_2: begin
				if (bram_ctrl_ready) begin
					// We finished storing the template vector.
					rxdata_retrieved = 1'b1;
				end
			end
			
			///////////////////////////////////////
			// Reading and storing input vector. //
			///////////////////////////////////////
			
			PREPARE_FOR_INPUT_VECTOR_1: begin
				// Clear the UART read buffer.
				rxdata_retrieved = 1'b1;
				
				// Ready the UART controller for transmission of acknowledgement.
				txdata = {120'b0, ACKNOWLEDGE};
				txcapture = 1'b1;
			end
			
			PREPARE_FOR_INPUT_VECTOR_2: begin
				// Transmit the acknowledgement to the BBB.
				txtransmit = 1'b1;
			end
			
			WAIT_FOR_INPUT_VECTOR_1: begin
				// Acknowledge completion of the transmission.
				if (txsent) begin
					txack = 1'b1;
				end
			end
			
			WAIT_FOR_INPUT_VECTOR_2: begin
				// Wait until the input vector arrives.
			end
		
			STORE_INPUT_VECTOR_2: begin
				if (bram_ctrl_ready) begin
					// We finished storing the input vector.
					rxdata_retrieved = 1'b1;
				end
			end
			
			///////////////////////////////////////
			// Reading and storing cycle vector. //
			///////////////////////////////////////
			
			PREPARE_FOR_CYCLE_VECTOR_1: begin
				// Clear the UART read buffer.
				rxdata_retrieved = 1'b1;
				
				// Ready the UART controller for transmission of acknowledgement.
				txdata = {120'b0, ACKNOWLEDGE};
				txcapture = 1'b1;
			end
			
			PREPARE_FOR_CYCLE_VECTOR_2: begin
				// Transmit the acknowledgement to the BBB.
				txtransmit = 1'b1;
			end
			
			WAIT_FOR_CYCLE_VECTOR_1: begin
				// Acknowledge completion of the transmission.
				if (txsent) begin
					txack = 1'b1;
				end
			end
			
			WAIT_FOR_CYCLE_VECTOR_2: begin
				// Wait until the cycle vector arrives.
			end
		
			STORE_CYCLE_VECTOR_2: begin
				if (bram_ctrl_ready) begin
					// We finished storing the input vector.
					rxdata_retrieved = 1'b1;
				end
			end
			
			//////////////////////////////////////////////
			// Reading and storing force-format vector. //
			//////////////////////////////////////////////
			
			PREPARE_FOR_FF_VECTOR_1: begin
				// Clear the UART read buffer.
				rxdata_retrieved = 1'b1;
				
				// Ready the UART controller for transmission of acknowledgement.
				txdata = {120'b0, ACKNOWLEDGE};
				txcapture = 1'b1;
			end
			
			PREPARE_FOR_FF_VECTOR_2: begin
				// Transmit the acknowledgement to the BBB.
				txtransmit = 1'b1;
			end
			
			WAIT_FOR_FF_VECTOR_1: begin
				// Acknowledge completion of the transmission.
				if (txsent) begin
					txack = 1'b1;
				end
			end
			
			WAIT_FOR_FF_VECTOR_2: begin
				// Wait until the FF vector arrives.
			end
			
			STORE_FF_VECTOR_2: begin
				if (bram_ctrl_ready) begin
					// We finished storing the input vector.
					rxdata_retrieved = 1'b1;
				end
			end
			
			///////////////////////////////
			// Cycle configuration data. //
			///////////////////////////////
			
			STORE_CYCLE_CONFIG_DATA: begin
				// Clear the UART read buffer.
				rxdata_retrieved = 1'b1;
			end
			
			/////////////////////////////////////////
			// Test completion and data retrieval. //
			/////////////////////////////////////////
			
			TESTS_COMPLETED: begin
				rxdata_retrieved = 1'b1;
			end
			
			TRANSMIT_SRAM_DATA: begin
				rxdata_retrieved = 1'b1;
			
				txdata = sram_data;
				txcapture = 1'b1;
			end
			
			/////////////////////////////////////
			// General UART code transmission. //
			/////////////////////////////////////
			
			UART_CAPTURE_ACK: begin
				txdata = {120'b0, ACKNOWLEDGE};
				txcapture = 1'b1;
			end
			
			UART_CAPTURE_UNKNOWN_CODE: begin
				// Clear the read buffer.
				rxdata_retrieved = 1'b1;
			
				txdata = {120'b0, UNKNOWN_CODE};
				txcapture = 1'b1;
			end
			
			UART_CAPTURE_NO_TESTS: begin
				// Clear the read buffer.
				rxdata_retrieved = 1'b1;
			
				txdata = {120'b0, NO_INPUT_VECTORS};
				txcapture = 1'b1;
			end
		
			UART_TRANSMIT_1: begin
				txtransmit = 1'b1;
			end
			
			UART_TRANSMIT_2: begin
				if (txsent) begin
					txack = 1'b1;
				end				
			end
			
		endcase
	end
	
	UART_CTRL uart_ctrl_0(
								 .CLK(CLK), 
								 .RST(RST), 
								 .RX(RX), 
								 .RXDATA_READY(rxdata_ready), 
								 .RXDATA_RETRIEVED(rxdata_retrieved), 
								 .RXDATA(rxdata), 
								 .TX(TX), 
								 .TXDATA(txdata), 
								 .TXCAPTURE(txcapture), 
								 .TXTRANSMIT(txtransmit), 
								 .TXSENT(txsent), 
								 .TXACK(txack)
								 );
	

	// Voltage translator controller.
	reg vt_en;
	
	always@(posedge CLK) begin
		if (RST) begin
			// The voltage translators output non-digital when placed in three-state.
			// We will leave them on unless we are reading from SRAM.
			vt_en <= 1'b1;
		end
		else begin
			case (PS) 
				IDLE: begin
					if (we_bar_in == 1'b0) begin // Safety measure
						vt_en <= 1'b1;
					end
				end
				
				LOAD_SRAM_DATA_0: begin
					// Turn off the voltage translators before we enable the SRAMs for read mode.
					vt_en <= 1'b0;
				end
				
				RESET_HARDWARE_PRETEST: begin
					vt_en <= 1'b1;
				end
			endcase
		end
	end
	
	// The voltage translators are always enabled except when
	// reading from the SRAM blocks, in which case they must be
	// disabled to prevent multiple-driver issues.
	VOLTAGE_TRANSLATOR_CTRL voltage_translator_ctrl(
																	.CLK(CLK),
																	.RST(RST),
																	.EN_IN(vt_en), 
																	.EN(VT_EN)
																	);

endmodule
