normgiff/Masters/explorations/clocking/NewReconfClockGen/clk_wiz_v3_6.v

// file: clk_wiz_v3_6.v
// 
// (c) Copyright 2008 - 2011 Xilinx, Inc. All rights reserved.
// 
// This file contains confidential and proprietary information
// of Xilinx, Inc. and is protected under U.S. and
// international copyright and other intellectual property
// laws.
// 
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
// CRITICAL APPLICATIONS
// Xilinx products are not designed or intended to be fail-
// safe, or for use in any application requiring fail-safe
// performance, such as life-support or safety devices or
// systems, Class III medical devices, nuclear facilities,
// applications related to the deployment of airbags, or any
// other applications that could lead to death, personal
// injury, or severe property or environmental damage
// (individually and collectively, "Critical
// Applications"). Customer assumes the sole risk and
// liability of any use of Xilinx products in Critical
// Applications, subject only to applicable laws and
// regulations governing limitations on product liability.
// 
// THIS COPYRIGHT NOTICE AND DISCLAIMER MUST BE RETAINED AS
// PART OF THIS FILE AT ALL TIMES.
// 
//----------------------------------------------------------------------------
// User entered comments
//----------------------------------------------------------------------------
// None
//
//----------------------------------------------------------------------------
// "Output    Output      Phase     Duty      Pk-to-Pk        Phase"
// "Clock    Freq (MHz) (degrees) Cycle (%) Jitter (ps)  Error (ps)"
//----------------------------------------------------------------------------
// CLK_OUT1___500.000______0.000______50.0_______97.082_____98.575
//
//----------------------------------------------------------------------------
// "Input Clock   Freq (MHz)    Input Jitter (UI)"
//----------------------------------------------------------------------------
// __primary_________100.000____________0.010

`timescale 1ps/1ps

(* CORE_GENERATION_INFO = "clk_wiz_v3_6,clk_wiz_v3_6,{component_name=clk_wiz_v3_6,use_phase_alignment=true,use_min_o_jitter=false,use_max_i_jitter=false,use_dyn_phase_shift=false,use_inclk_switchover=false,use_dyn_reconfig=false,feedback_source=FDBK_AUTO,primtype_sel=MMCM_ADV,num_out_clk=1,clkin1_period=10.000,clkin2_period=10.000,use_power_down=false,use_reset=true,use_locked=true,use_inclk_stopped=false,use_status=false,use_freeze=false,use_clk_valid=false,feedback_type=SINGLE,clock_mgr_type=MANUAL,manual_override=false}" *)
module clk_wiz_v3_6
 (// Clock in ports
  input         CLK_IN,
  // Clock out ports
  output        CLK_OUT,
  // Status and control signals
  input         RESET,
  output        LOCKED
 );

  // Input buffering
  //------------------------------------
  IBUFG clkin1_buf
   (.O (clkin1),
    .I (CLK_IN));


  // Clocking primitive
  //------------------------------------
  // Instantiation of the MMCM primitive
  //    * Unused inputs are tied off
  //    * Unused outputs are labeled unused
  wire [15:0] do_unused;
  wire        drdy_unused;
  wire        psdone_unused;
  wire        clkfbout;
  wire        clkfbout_buf;
  wire        clkfboutb_unused;
  wire        clkout0b_unused;
  wire        clkout1_unused;
  wire        clkout1b_unused;
  wire        clkout2_unused;
  wire        clkout2b_unused;
  wire        clkout3_unused;
  wire        clkout3b_unused;
  wire        clkout4_unused;
  wire        clkout5_unused;
  wire        clkout6_unused;
  wire        clkfbstopped_unused;
  wire        clkinstopped_unused;

  MMCME2_ADV
  #(.BANDWIDTH            ("OPTIMIZED"),
    .CLKOUT4_CASCADE      ("FALSE"),
    .COMPENSATION         ("ZHOLD"),
    .STARTUP_WAIT         ("FALSE"),
    .DIVCLK_DIVIDE        (1),
    .CLKFBOUT_MULT_F      (10.000),
    .CLKFBOUT_PHASE       (0.000),
    .CLKFBOUT_USE_FINE_PS ("FALSE"),
    .CLKOUT0_DIVIDE_F     (2.000),
    .CLKOUT0_PHASE        (0.000),
    .CLKOUT0_DUTY_CYCLE   (0.500),
    .CLKOUT0_USE_FINE_PS  ("FALSE"),
    .CLKIN1_PERIOD        (10.000),
    .REF_JITTER1          (0.010))
  mmcm_adv_inst
    // Output clocks
   (.CLKFBOUT            (clkfbout),
    .CLKFBOUTB           (clkfboutb_unused),
    .CLKOUT0             (clkout0),
    .CLKOUT0B            (clkout0b_unused),
    .CLKOUT1             (clkout1_unused),
    .CLKOUT1B            (clkout1b_unused),
    .CLKOUT2             (clkout2_unused),
    .CLKOUT2B            (clkout2b_unused),
    .CLKOUT3             (clkout3_unused),
    .CLKOUT3B            (clkout3b_unused),
    .CLKOUT4             (clkout4_unused),
    .CLKOUT5             (clkout5_unused),
    .CLKOUT6             (clkout6_unused),
     // Input clock control
    .CLKFBIN             (clkfbout_buf),
    .CLKIN1              (clkin1),
    .CLKIN2              (1'b0),
     // Tied to always select the primary input clock
    .CLKINSEL            (1'b1),
    // Ports for dynamic reconfiguration
    .DADDR               (7'h0),
    .DCLK                (1'b0),
    .DEN                 (1'b0),
    .DI                  (16'h0),
    .DO                  (do_unused),
    .DRDY                (drdy_unused),
    .DWE                 (1'b0),
    // Ports for dynamic phase shift
    .PSCLK               (1'b0),
    .PSEN                (1'b0),
    .PSINCDEC            (1'b0),
    .PSDONE              (psdone_unused),
    // Other control and status signals
    .LOCKED              (LOCKED),
    .CLKINSTOPPED        (clkinstopped_unused),
    .CLKFBSTOPPED        (clkfbstopped_unused),
    .PWRDWN              (1'b0),
    .RST                 (RESET));

  // Output buffering
  //-----------------------------------
  BUFG clkf_buf
   (.O (clkfbout_buf),
    .I (clkfbout));

  BUFG clkout1_buf
   (.O   (CLK_OUT),
    .I   (clkout0));

endmodule
