normgiff/Masters/Verilog/ASICTesterVerilog/DB_FF_REG.v

`timescale 1ns / 1ps

/*
 * Module:            DB_FF_REG
 * Function:          A FF_REG that is preceded by a register.
 * 
 * Inputs: 
 *    CLK
 *    RST
 *    EN_FF_LOGIC:    Active-high enable for counting cycles (see FF_REG.v).
 *    LOAD_FF:        Loads the FF value into a buffer in this module.
 *    TRANSFER_FF:    "Activates" the buffered FF value.
 *    FF: 		       0 == R0 		(see FF_REG.v)
 * 				       1 == DNRZ_L	(see FF_REG.v)
 *    LOAD_SIG:       Loads the signal value D into a buffer in this module.
 *    TRANSFER_SIG:   "Activates" the buffered signal value.
 * 	D
 *    LEADING_EDGE_1:  One possible leading edge value, determined by TEST_CYCLE.
 *    LEADING_EDGE_2:  One possible leading edge value, determined by TEST_CYCLE.
 *    TRAILING_EDGE:   Trailing edge value. (Number of clock cycles to count before 
 *                     trailing edge occurs.)
 *    CYCLE_LENGTH:    Number of clock cycles comprising a single test cycle.
 *    TEST_CYCLE:      Determines whether to use LEADING_EDGE_1 or LEADING_EDGE_2.
 * Outputs:
 * 	Q
 */ 
module FF_DB_REG(CLK, RST, EN_FF_LOGIC, LOAD_FF, TRANSFER_FF, FF, 
					  LOAD_SIG, TRANSFER_SIG, D,
					  LEADING_EDGE_1, LEADING_EDGE_2, TRAILING_EDGE, CYCLE_LENGTH,
					  TEST_CYCLE, Q);
	input CLK;
	input RST;
	input EN_FF_LOGIC;
	
	input LOAD_FF;
	input TRANSFER_FF;
	
	input FF;
	input D;
	
	input LOAD_SIG;
	input TRANSFER_SIG;
	
	input [9:0] LEADING_EDGE_1;
	input [9:0] LEADING_EDGE_2;
	input [9:0] TRAILING_EDGE;
	input [9:0] CYCLE_LENGTH;
	
	input TEST_CYCLE;
	
	output Q;
	
	reg buffer_data;
	reg buffer_out;
	
	reg ff_data;
	reg ff_out;

	wire [9:0] leading_edge;
	
	assign leading_edge = (TEST_CYCLE) ? LEADING_EDGE_2 : LEADING_EDGE_1;

	FF_REG ff_reg0(.CLK(CLK), .RST(RST), .EN(EN_FF_LOGIC), .LEADING_EDGE(leading_edge), 
						.TRAILING_EDGE(TRAILING_EDGE), .CYCLE_LENGTH(CYCLE_LENGTH), 
						.D(buffer_out), .FF(ff_out), .Q(Q));	
	
	always@(posedge CLK) begin
		if (RST) begin
			buffer_data <= 1'b0;
			buffer_out <= 1'b0;
			ff_data <= 1'b0;
			ff_out <= 1'b0;
		end
		else begin
			if (LOAD_SIG) begin
				buffer_data <= D;
			end
			if (LOAD_FF) begin
				ff_data <= FF;
			end
			if (TRANSFER_SIG) begin
				buffer_out <= buffer_data;
			end
			if (TRANSFER_FF) begin
				ff_out <= ff_data;
			end
		end
	end

endmodule
