normgiff/Masters/Verilog/ASICTesterVerilog/CENTRAL_FSM_PARAMS.v

// UART codes (from BeagleBone Black)
parameter TEMPLATE_HDR       = 8'b00000000;
parameter FF_HDR             = 8'b00000001;
parameter CYCLE_HDR          = 8'b00000010;
parameter INPUT_HDR          = 8'b00000011;
parameter CYCLE_CONFIG_HDR   = 8'b00000100;
parameter EXECUTE_TESTS      = 8'b00000101;
parameter SEND_BACK_DATA     = 8'b00000110;

// UART codes (to BeagleBone Black)
parameter ACKNOWLEDGE        = 8'b00000000;
parameter NO_INPUT_VECTORS   = 8'b00000001;
parameter UNKNOWN_CODE       = 8'b11111111; 

// States
parameter IDLE = 6'd0;
parameter DECODE_UART_CODE = 6'd1;
parameter PREPARE_FOR_TEMPLATE_VECTOR_1 = 6'd2;
parameter PREPARE_FOR_TEMPLATE_VECTOR_2 = 6'd3;
parameter WAIT_FOR_TEMPLATE_VECTOR_1 = 6'd4;
parameter WAIT_FOR_TEMPLATE_VECTOR_2 = 6'd5;
parameter STORE_TEMPLATE_VECTOR_1 = 6'd6;
parameter STORE_TEMPLATE_VECTOR_2 = 6'd7;
parameter PREPARE_FOR_INPUT_VECTOR_1 = 8;
parameter PREPARE_FOR_INPUT_VECTOR_2 = 6'd9;
parameter WAIT_FOR_INPUT_VECTOR_1 = 6'd10;
parameter WAIT_FOR_INPUT_VECTOR_2 = 6'd11; 
parameter STORE_INPUT_VECTOR_1 = 6'd12;
parameter STORE_INPUT_VECTOR_2 = 6'd13;
parameter PREPARE_FOR_CYCLE_VECTOR_1 = 6'd14;
parameter PREPARE_FOR_CYCLE_VECTOR_2 = 6'd15;
parameter WAIT_FOR_CYCLE_VECTOR_1 = 6'd16;
parameter WAIT_FOR_CYCLE_VECTOR_2 = 6'd17;
parameter STORE_CYCLE_VECTOR_1 = 6'd18;
parameter STORE_CYCLE_VECTOR_2 = 6'd19;
parameter PREPARE_FOR_FF_VECTOR_1 = 6'd20;
parameter PREPARE_FOR_FF_VECTOR_2 = 6'd21;
parameter WAIT_FOR_FF_VECTOR_1 = 6'd22;
parameter WAIT_FOR_FF_VECTOR_2 = 6'd23;
parameter STORE_FF_VECTOR_1 = 6'd24;
parameter STORE_FF_VECTOR_2 = 6'd25;
parameter STORE_CYCLE_CONFIG_DATA = 6'd26;
parameter RESET_HARDWARE_PRETEST = 6'd27;
parameter READ_INPUT_VECTOR_1 = 6'd28;
parameter READ_INPUT_VECTOR_2 = 6'd29;
parameter LOAD_INPUT_VECTOR = 6'd30;
parameter TRANSFER_INPUT_VECTOR = 6'd31;
parameter READ_TEMPLATE_VECTOR_1 = 6'd32;
parameter READ_TEMPLATE_VECTOR_2 = 6'd33;
parameter LOAD_TEMPLATE_VECTOR = 6'd34;
parameter READ_CYCLE_VECTOR_1 = 6'd35;
parameter READ_CYCLE_VECTOR_2 = 6'd36;
parameter LOAD_CYCLE_VECTOR = 6'd37;
parameter READ_FF_VECTOR_1 = 6'd38;
parameter READ_FF_VECTOR_2 = 6'd39;
parameter LOAD_FF_VECTOR = 6'd40;
parameter TRANSFER_VECTORS = 6'd41;
parameter CHECK_FOR_MORE_INPUT_VECTORS = 6'd42;
parameter CHECK_INPUT_VECTOR = 6'd43;
parameter TESTS_COMPLETED = 6'd44;
parameter LOAD_SRAM_DATA_0 = 6'd45;
parameter LOAD_SRAM_DATA_1 = 6'd46;
parameter LOAD_SRAM_DATA_2 = 6'd47;
parameter LOAD_SRAM_DATA_3 = 6'd48;
parameter LOAD_SRAM_DATA_4 = 6'd49;
parameter LOAD_SRAM_DATA_5 = 6'd50;
parameter TRANSMIT_SRAM_DATA = 6'd51;
parameter UART_CAPTURE_ACK = 6'd52;
parameter UART_CAPTURE_UNKNOWN_CODE = 6'd53;
parameter UART_CAPTURE_NO_TESTS = 6'd54;
parameter UART_TRANSMIT_1 = 6'd55;
parameter UART_TRANSMIT_2 = 6'd56;
